joaramirezra/Fitotron/firmware/EsquemaFitotron.png

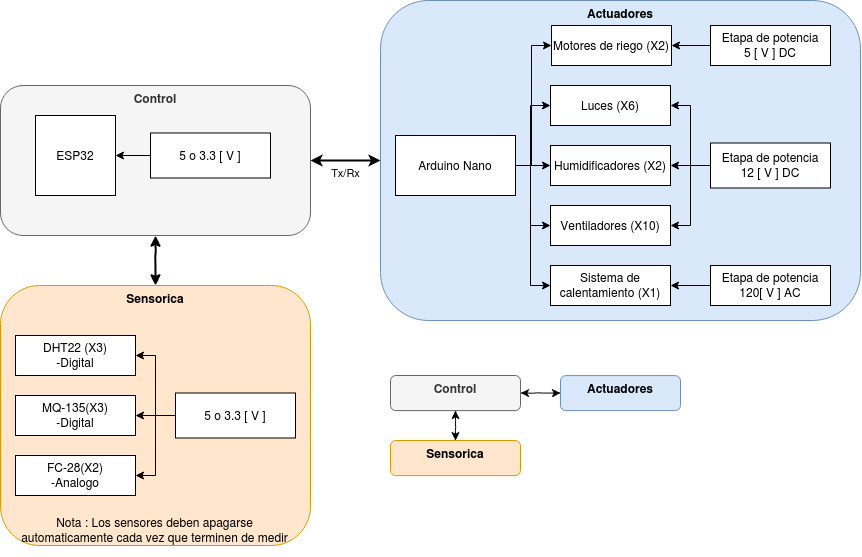
firmware/EsquemaFitotron.png
